Mathimix7/HueMix-Link/Hardware-designs/Gateway_v1.1/Gateway_v1.1_back.png

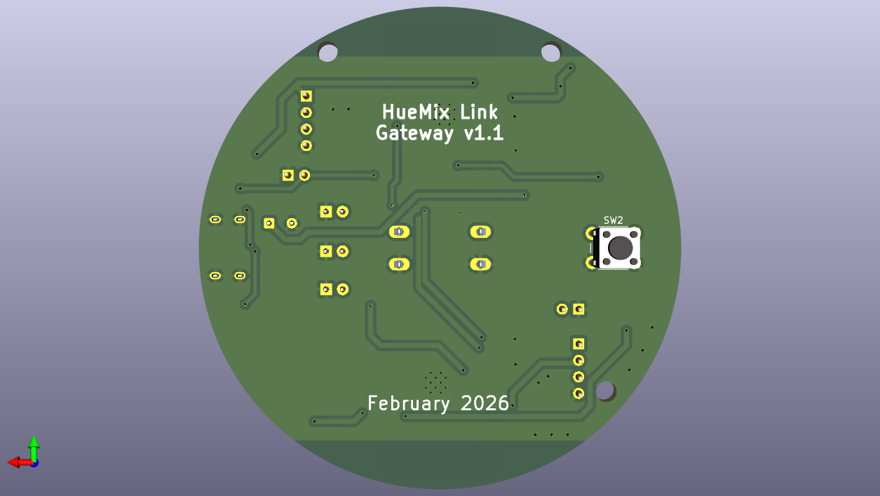
Hardware-designs/Gateway_v1.1/Gateway_v1.1_back.png
