Mathimix7/HueMix-Link/Hardware-designs/Magnetic Sensor/Magnetic Sensor-front.png

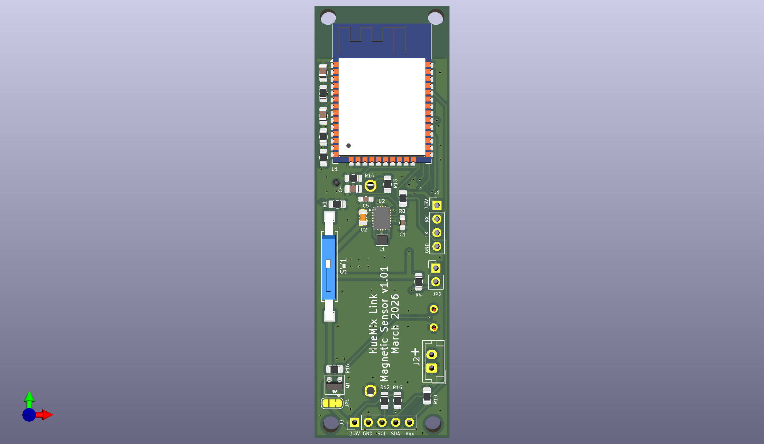
Hardware-designs/Magnetic Sensor/Magnetic Sensor-front.png
