Mathimix7/HueMix-Link/Hardware-designs/Motion_Sensor_v1.1/Motion_Sensor_v1.1_front.png

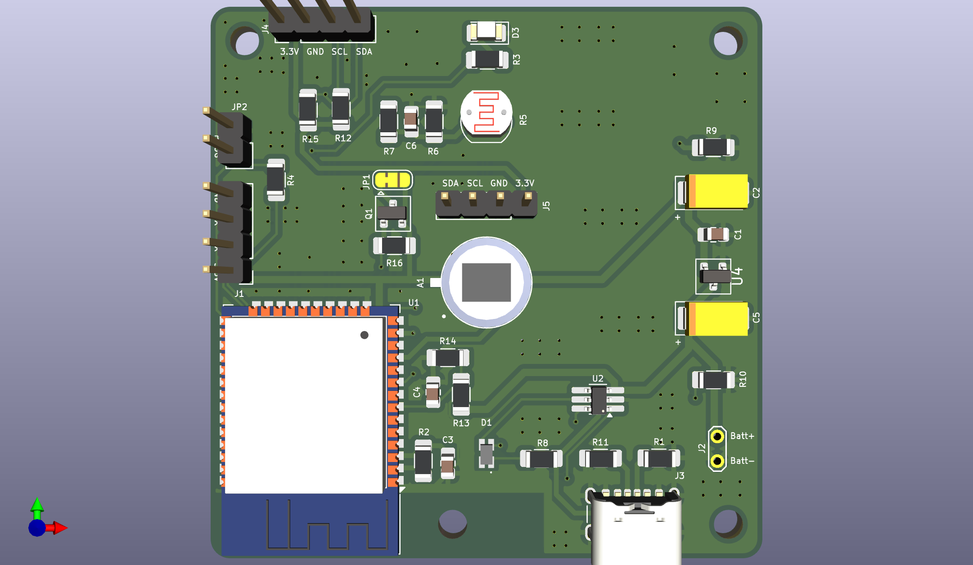
Hardware-designs/Motion_Sensor_v1.1/Motion_Sensor_v1.1_front.png
