Mathimix7/HueMix-Link/Hardware-designs/Normal_Button_v3/Normal_Button_v3_back.png

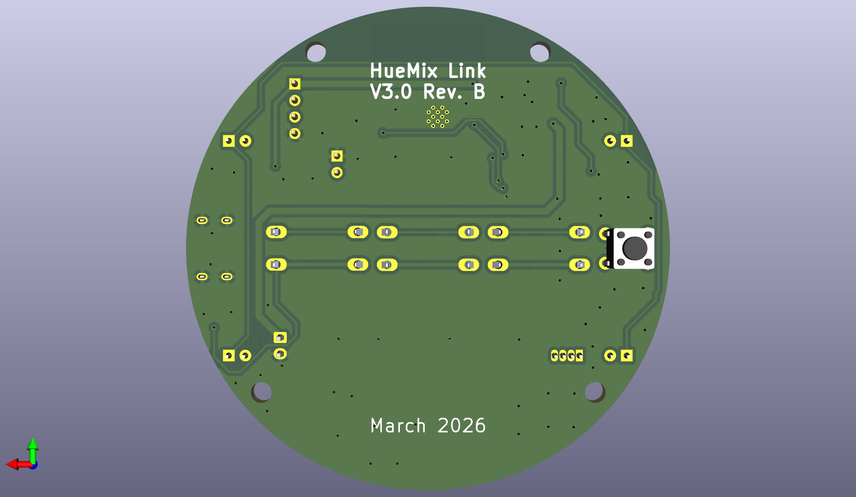
Hardware-designs/Normal_Button_v3/Normal_Button_v3_back.png
