Mathimix7/HueMix-Link/Hardware-designs/Magnetic Sensor/components/C1608X5R1A226M080AC/C1608X5R1A226M080AC.step

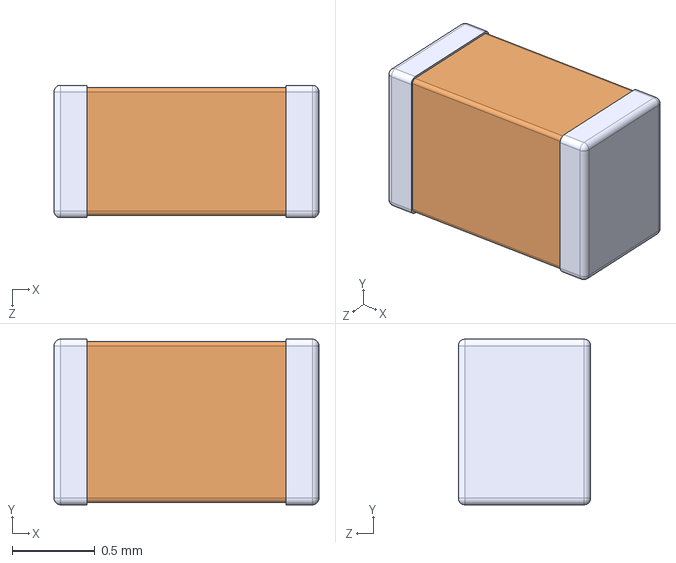
[picture p44: CAD file, 2026-03-12]
Hardware-designs/Magnetic Sensor/components/C1608X5R1A226M080AC/C1608X5R1A226M080AC.step
1.60 x 1.00 x 0.8 mm
