Mathimix7/HueMix-Link/Hardware-designs/Magnetic Sensor/components/IRA_S410ST01/IRA-S410ST01.step

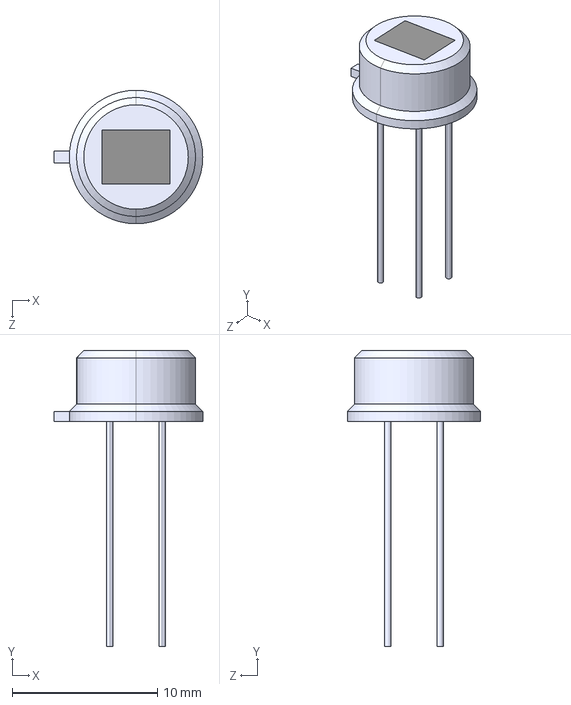
[picture p45: CAD file, 2026-02-21]
Hardware-designs/Magnetic Sensor/components/IRA_S410ST01/IRA-S410ST01.step
10.2 x 20.4 x 9.20 mm
