Mathimix7/HueMix-Link/Hardware-designs/Magnetic Sensor/components/MCP1700T_3302E_MB/SOT-23_MC_MCH.step

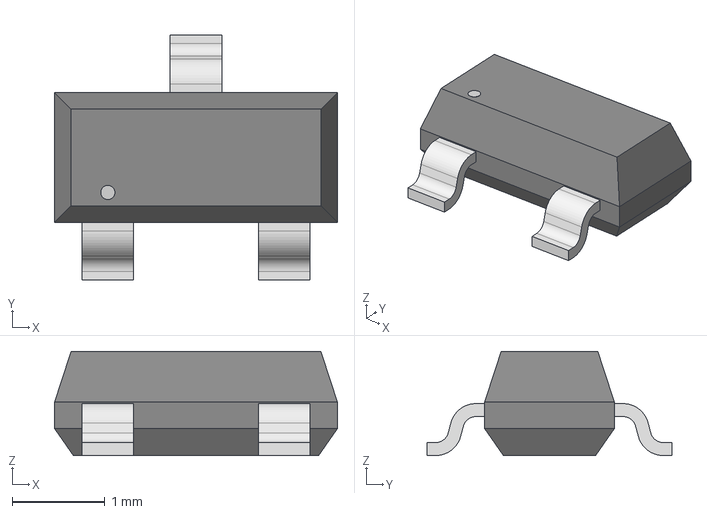
[picture p46: CAD file, 2026-02-21]
Hardware-designs/Magnetic Sensor/components/MCP1700T_3302E_MB/SOT-23_MC_MCH.step
3.05 x 2.64 x 1.12 mm
