Mathimix7/HueMix-Link/Hardware-designs/Magnetic Sensor/components/MSASJ21GBB5476MTNA01/MSASJ21GBB5476MTNA01.step

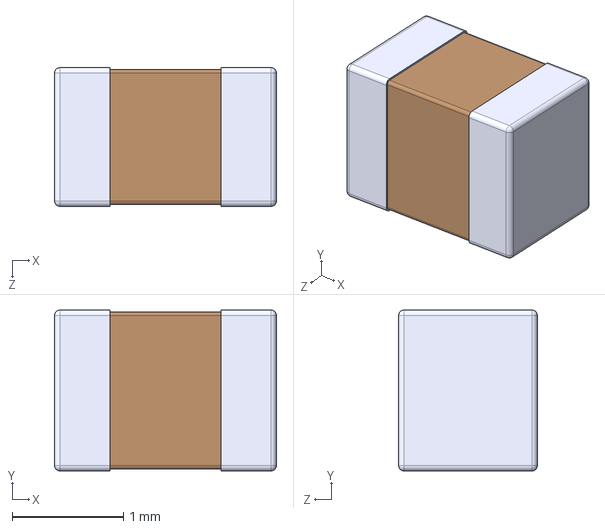
[picture p47: CAD file, 2026-03-12]
Hardware-designs/Magnetic Sensor/components/MSASJ21GBB5476MTNA01/MSASJ21GBB5476MTNA01.step
2.00 x 1.45 x 1.25 mm
