Mathimix7/HueMix-Link/Hardware-designs/Magnetic Sensor/components/Tantalum Cap/TAJC227K006RNJ.STEP

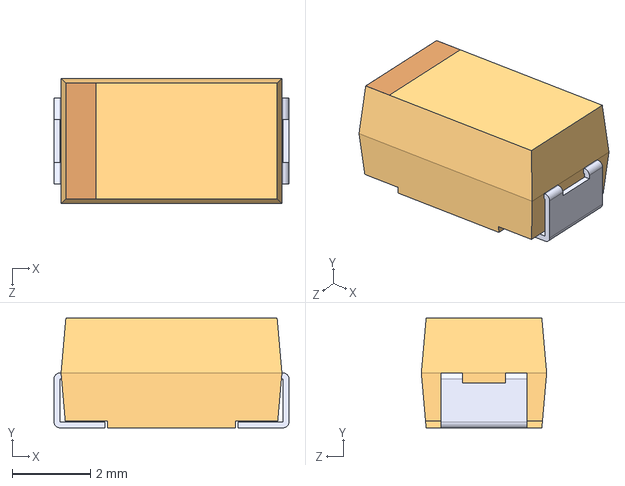
[picture p48: CAD file, 2026-02-21]
Hardware-designs/Magnetic Sensor/components/Tantalum Cap/TAJC227K006RNJ.STEP
6.00 x 2.80 x 3.20 mm
