Mathimix7/HueMix-Link/Hardware-designs/Magnetic Sensor/Magnetic Sensor.step

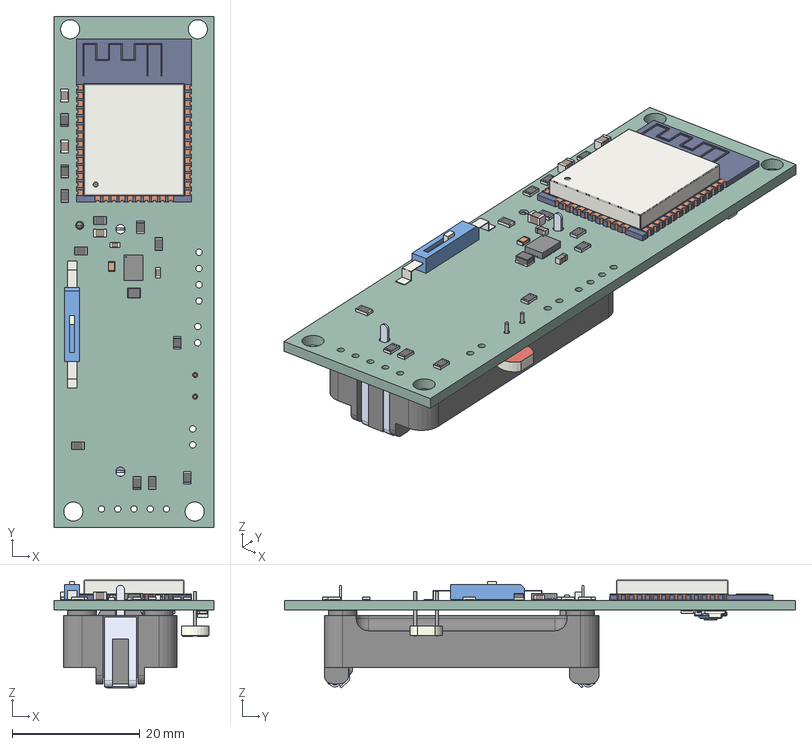
[picture p49: CAD file, 2026-03-29]
Hardware-designs/Magnetic Sensor/Magnetic Sensor.step
25.0 x 80.0 x 16.9 mm
L_Murata_DFE201610P
C1608X5R1A226M080AC
ESP32-WROOM-32
C_0805_2012Metric x 3
R_0805_2012Metric x 14
TPS63021DSJR
C_0603_1608Metric x 2
SW_SPST_REED_CT10_XXXX_G003
SW_SPST_REED_CT10_XXXX_G2
BH123A
R_LDR_5.1x4.3mm_P3.4mm_Vertical
PTS526SK15SMTR2_LFS
LED_1206_3216Metric
Magnetic Sensor_PCB
