Mathimix7/HueMix-Link/Hardware-designs/Motion_Sensor_v1.1/Motion_Sensor_v1.1.step

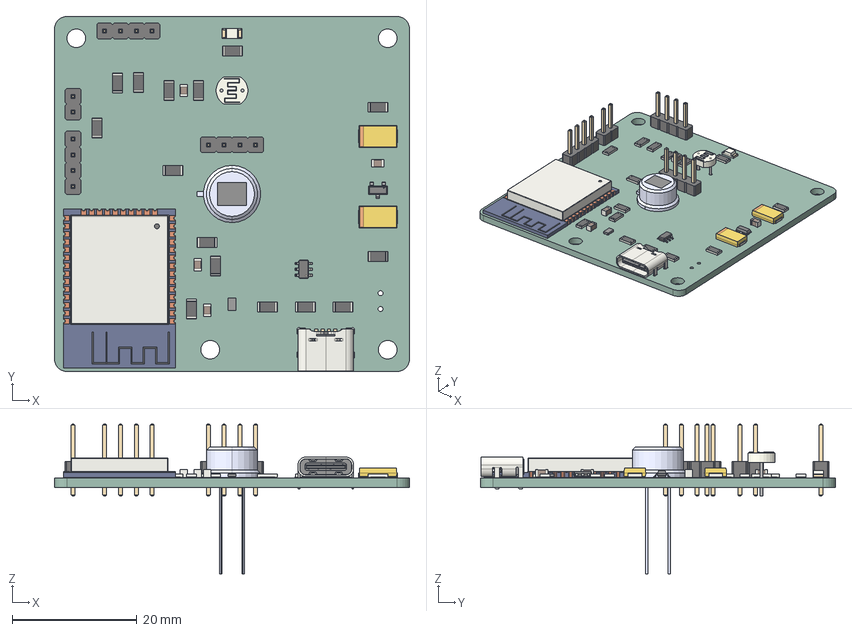
[picture p50: CAD file, 2026-02-21]
Hardware-designs/Motion_Sensor_v1.1/Motion_Sensor_v1.1.step
57.0 x 57.0 x 24.0 mm
R_1206_3216Metric x 15
C_0805_2012Metric x 4
USB_C_Receptacle_GCT_USB4125-xx-x-0190_6P_TopMnt_Horizontal
TSOT-23-6
LED_1206_3216Metric
PinHeader_1x02_P2.54mm_Vertical
IRA-S410ST01
CP_EIA-6032-15_Kemet-U x 2
SOT-23_MC_MCH
ESP32-WROOM-32
PinHeader_1x04_P2.54mm_Vertical x 3
R_LDR_5.1x4.3mm_P3.4mm_Vertical
Pins
Motion_Sensor_v1.1_PCB
