Mathimix7/HueMix-Link/Hardware-designs/Normal_Button_v3/components/ESP32 3D/ESP32-WROOM-32E-N8.STEP

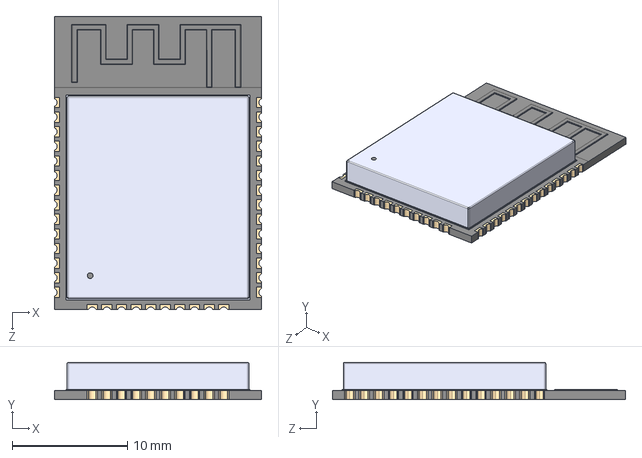
[picture p51: CAD file, 2026-02-21]
Hardware-designs/Normal_Button_v3/components/ESP32 3D/ESP32-WROOM-32E-N8.STEP
18.0 x 3.25 x 25.5 mm
