Mathimix7/HueMix-Link/Hardware-designs/Normal_Button_v3/Normal_Button_v3.step

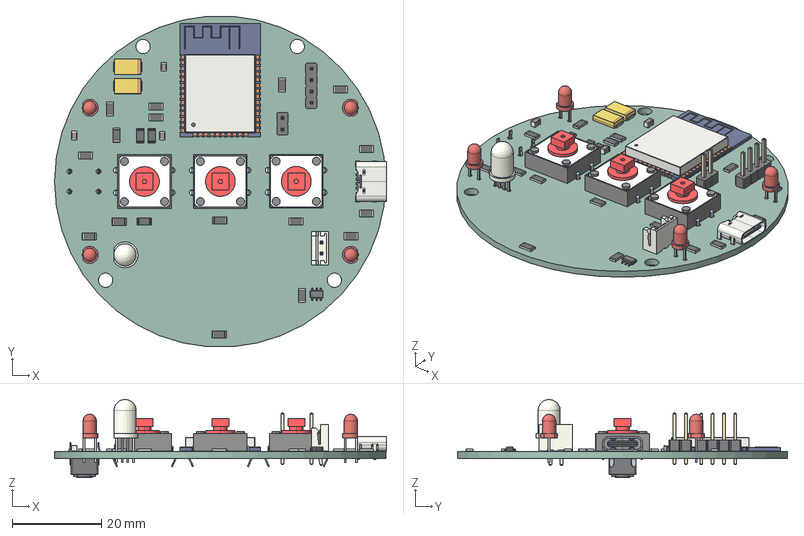
[picture p52: CAD file, 2026-03-01]
Hardware-designs/Normal_Button_v3/Normal_Button_v3.step
74.3 x 74.0 x 17.5 mm
R_1206_3216Metric x 19
TSOT-23-6
USB_C_Receptacle_GCT_USB4125-xx-x-0190_6P_TopMnt_Horizontal
LED_D3.0mm x 4
PinHeader_1x04_P2.54mm_Vertical
SW_PUSH_6mm
Body002 (Mirror #1) x 3
Body003 (Mirror #2) x 3
CP_EIA-6032-15_Kemet-U x 2
C_0805_2012Metric x 3
ESP32-WROOM-32
PinHeader_1x02_P2.54mm_Vertical
LED_D5.0mm-4_RGB
JST_EH_B2B-EH-A_1x02_P2.50mm_Vertical
Normal_Button_v3_PCB
