Mathimix7/HueMix-Link/Hardware-designs/Remote_4button_v1/Remote_4button_v1.step

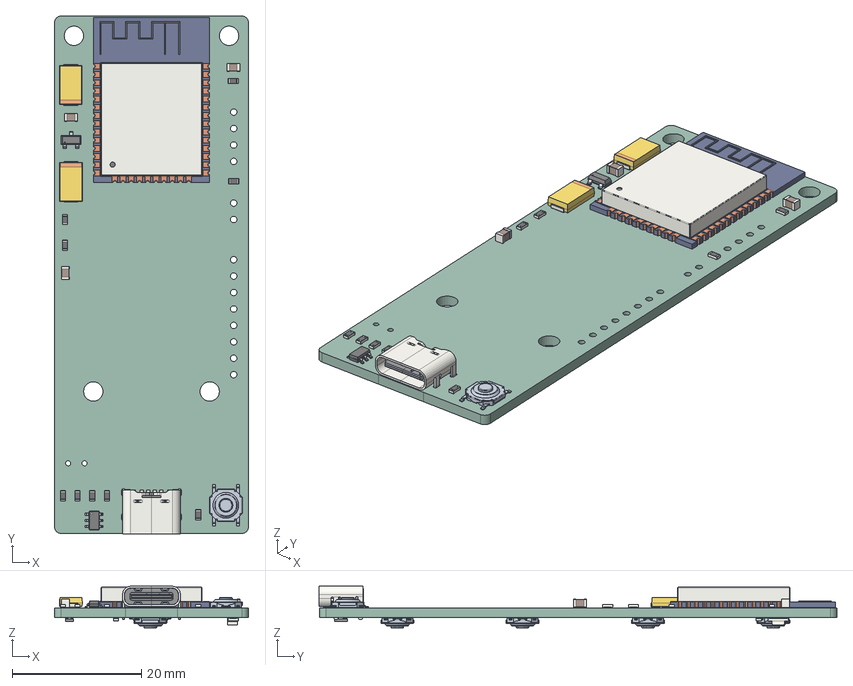
[picture p53: CAD file, 2026-02-21]
Hardware-designs/Remote_4button_v1/Remote_4button_v1.step
30.0 x 80.1 x 6.44 mm
R_0603_1608Metric x 14
C_0805_2012Metric x 3
USB_C_Receptacle_GCT_USB4125-xx-x-0190_6P_TopMnt_Horizontal
PTS526SK15SMTR2_LFS x 5
TSOT-23-6
CP_EIA-6032-15_Kemet-U x 2
SOT-23_MC_MCH
ESP32-WROOM-32
LED_1206_3216Metric
Pins
Remote_4button_v1_PCB
