Mathimix7/HueMix-Link/3D Files/Buttons/1_Button/Lid_1_Button.stl

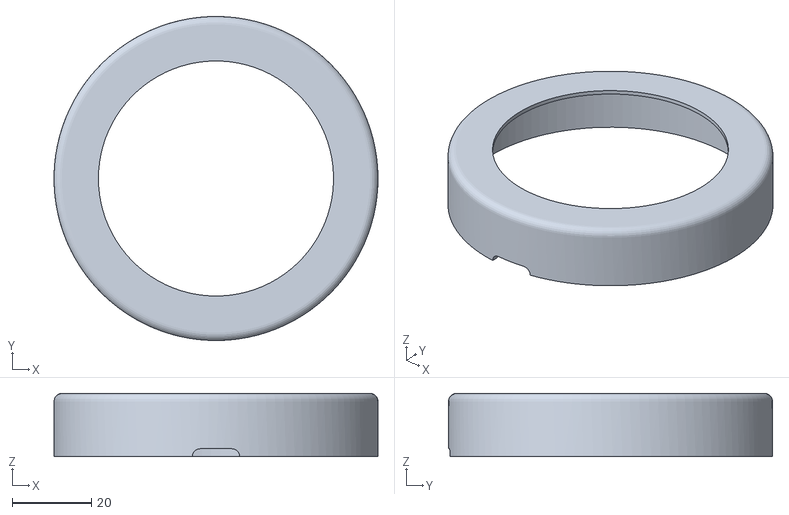
[picture p54: CAD file, 2026-04-03]
3D Files/Buttons/1_Button/Lid_1_Button.stl
82.0 x 82.0 x 16.0
