Mathimix7/HueMix-Link/3D Files/Door Sensor/Box Magnetic Sensor.stl

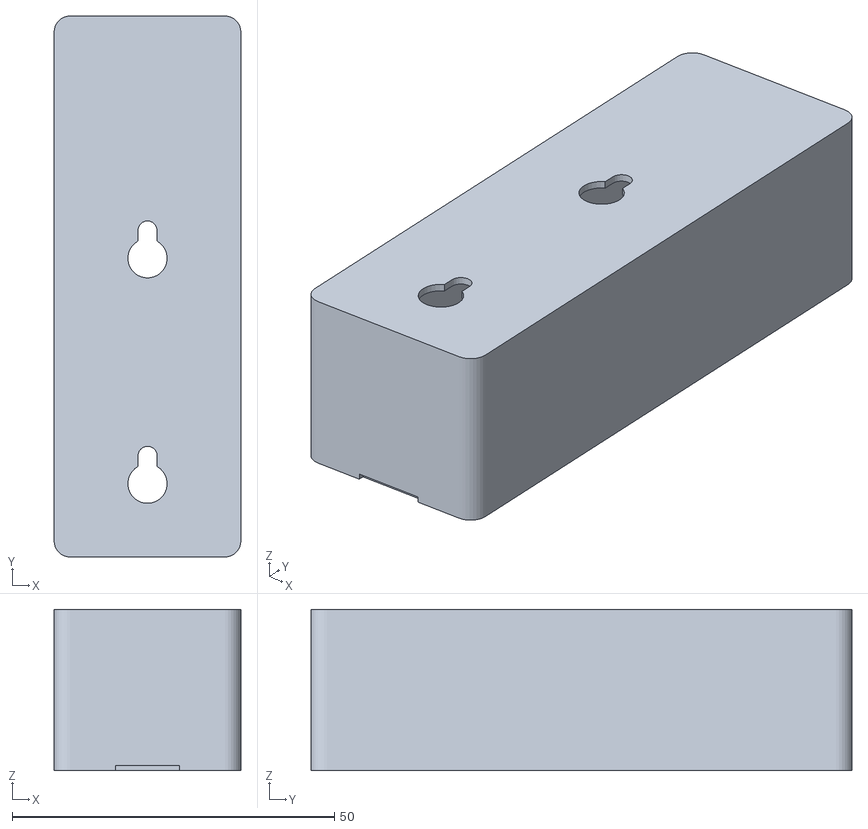
[picture p55: CAD file, 2026-04-03]
3D Files/Door Sensor/Box Magnetic Sensor.stl
29.0 x 84.0 x 25.0
