Mathimix7/HueMix-Link/3D Files/Lightstrip/Lid Lightstrip controller.stl

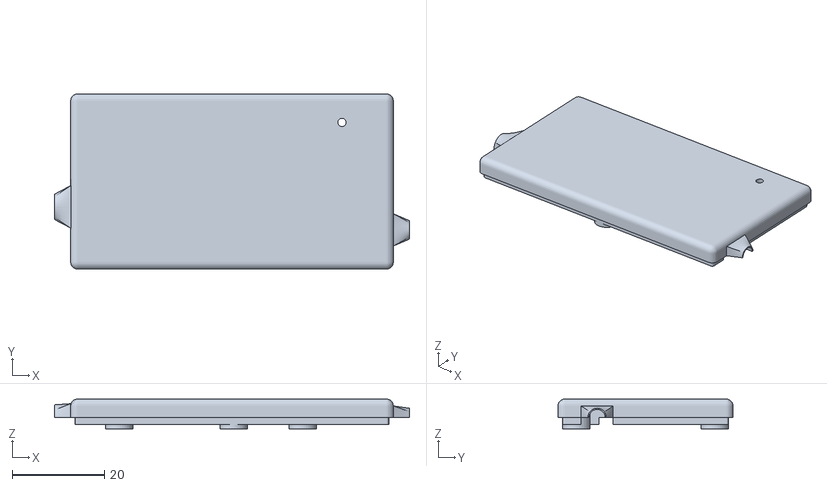
[picture p56: CAD file, 2026-04-03]
3D Files/Lightstrip/Lid Lightstrip controller.stl
77.0 x 38.0 x 6.50
