Mathimix7/HueMix-Link/3D Files/Motion Sensor/Holder Motion Sensor_slim.stl

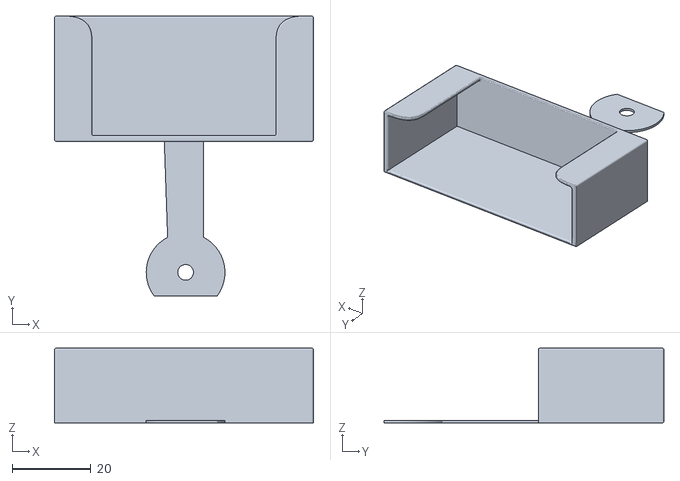
[picture p57: CAD file, 2026-04-03]
3D Files/Motion Sensor/Holder Motion Sensor_slim.stl
65.8 x 71.1 x 19.0
