Mathimix7/HueMix-Link/3D Files/Remote/Remote Base.stl

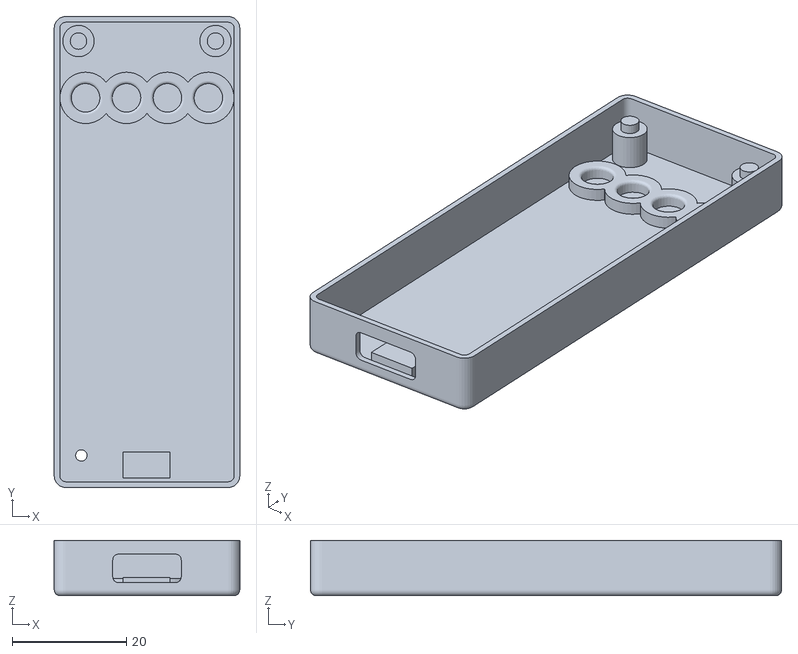
[picture p58: CAD file, 2026-04-03]
3D Files/Remote/Remote Base.stl
32.5 x 82.5 x 9.70
