Mathimix7/HueMix-Link/3D Files/Buttons/1_Button/Axle_1_Button.stl

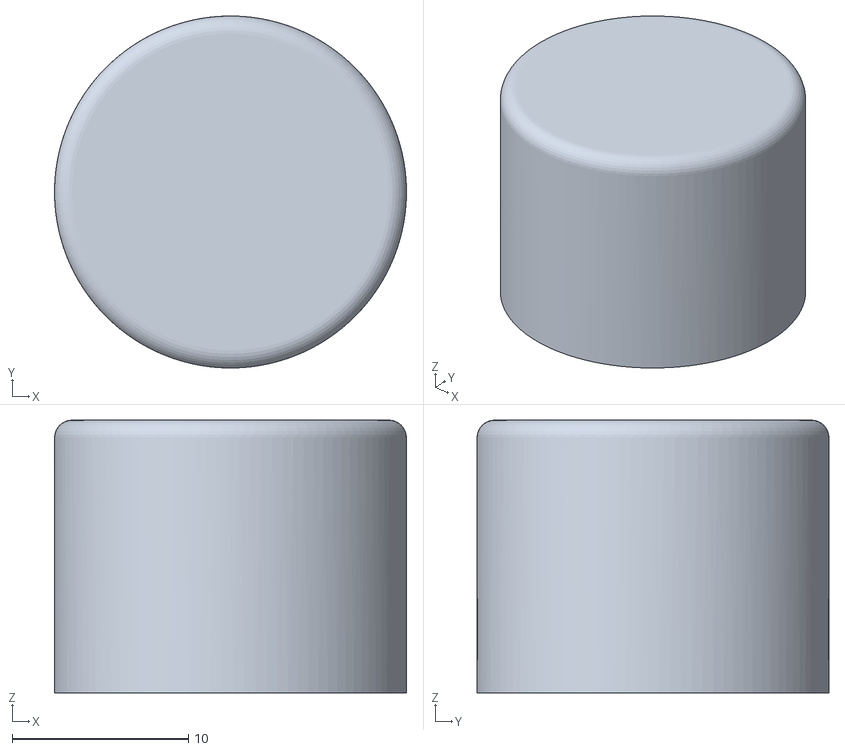
[picture p59: CAD file, 2026-04-03]
3D Files/Buttons/1_Button/Axle_1_Button.stl
20.0 x 20.0 x 15.5
