Mathimix7/HueMix-Link/3D Files/Buttons/2_Button/Square button_2 buttons.stl

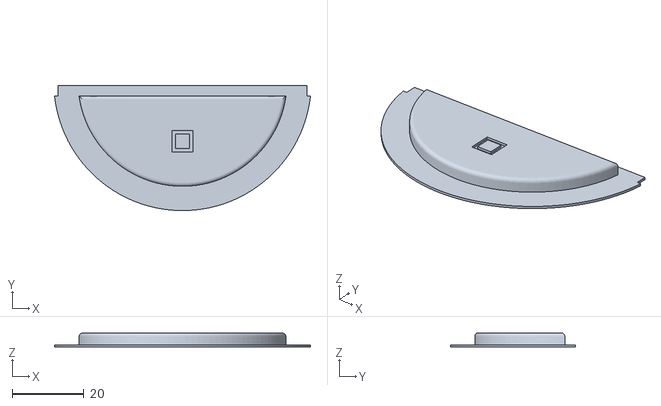
[picture p60: CAD file, 2026-04-03]
3D Files/Buttons/2_Button/Square button_2 buttons.stl
71.6 x 35.0 x 4.00
