Mathimix7/HueMix-Link/3D Files/Door Sensor/Holder Magnetic Sensor.stl

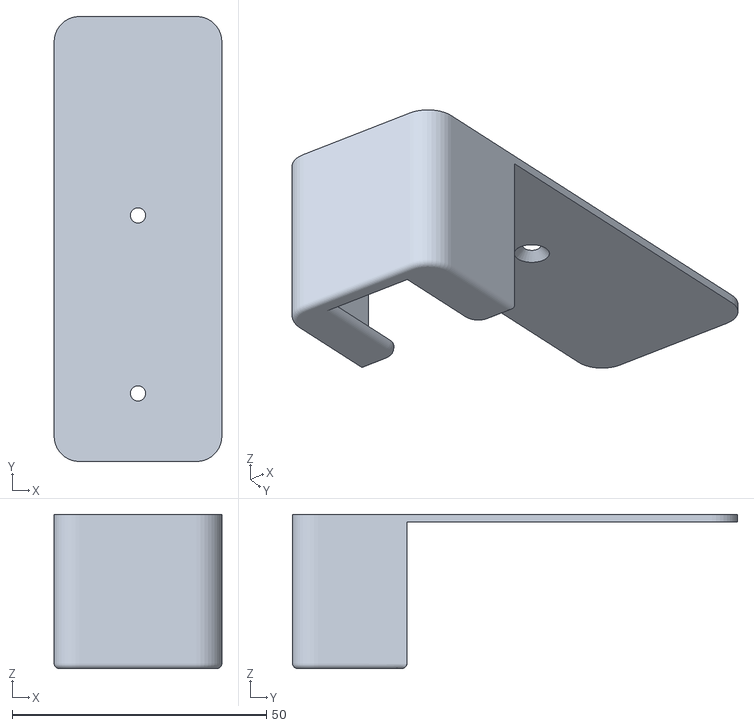
[picture p61: CAD file, 2026-04-03]
3D Files/Door Sensor/Holder Magnetic Sensor.stl
33.0 x 87.5 x 30.3
