Mathimix7/HueMix-Link/3D Files/Motion Sensor/Base Motion Sensor.stl

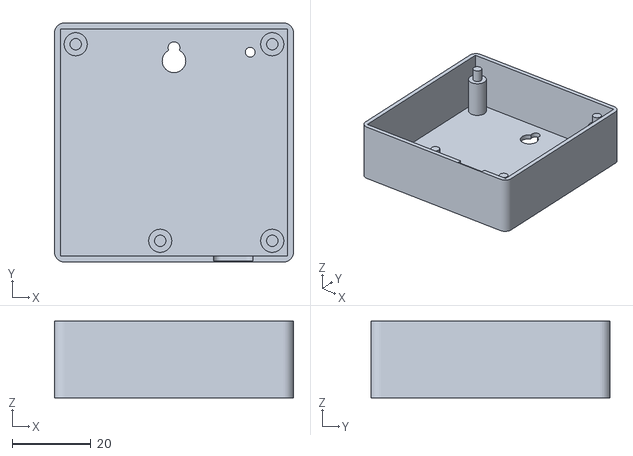
[picture p62: CAD file, 2026-04-03]
3D Files/Motion Sensor/Base Motion Sensor.stl
60.8 x 60.8 x 19.5
