Mathimix7/HueMix-Link/3D Files/Remote/Remote Lid.stl

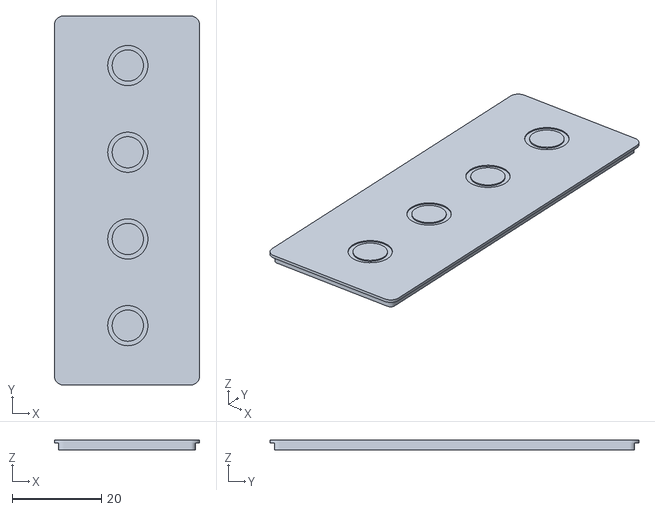
[picture p63: CAD file, 2026-04-03]
3D Files/Remote/Remote Lid.stl
32.5 x 82.5 x 2.20
