Mathimix7/HueMix-Link/3D Files/Buttons/3_Button/Lid_3 buttons.stl

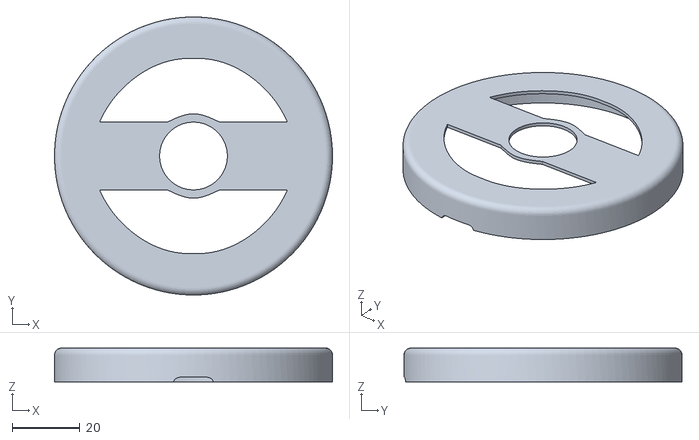
[picture p65: CAD file, 2026-04-03]
3D Files/Buttons/3_Button/Lid_3 buttons.stl
82.0 x 82.0 x 10.0
