Mathimix7/HueMix-Link/3D Files/Motion Sensor/Base Motion Sensor_slim.stl

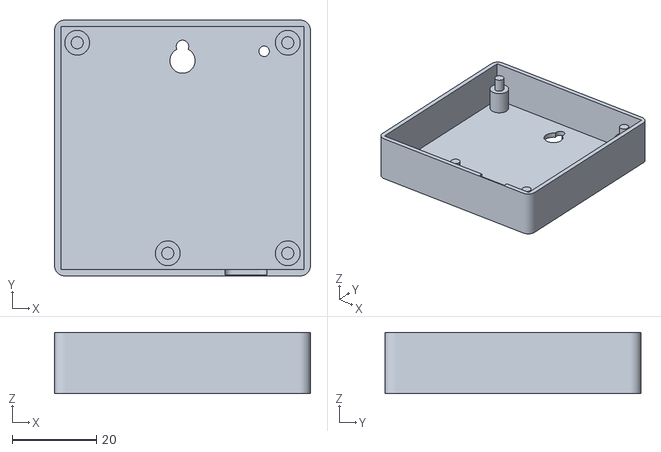
[picture p66: CAD file, 2026-04-03]
3D Files/Motion Sensor/Base Motion Sensor_slim.stl
60.8 x 60.8 x 14.5
