Mathimix7/HueMix-Link/3D Files/Buttons/3_Button/Square button_3 buttons.stl

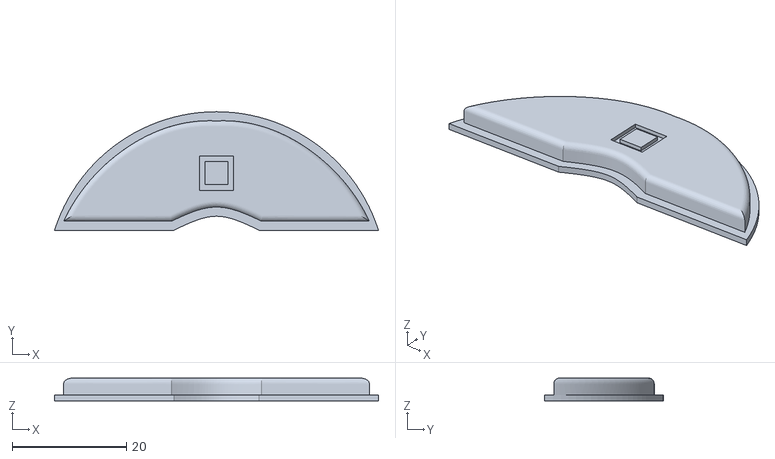
[picture p67: CAD file, 2026-04-03]
3D Files/Buttons/3_Button/Square button_3 buttons.stl
56.7 x 20.8 x 4.00
