Mathimix7/HueMix-Link/3D Files/Buttons/2_Button/Lid_2 buttons.stl

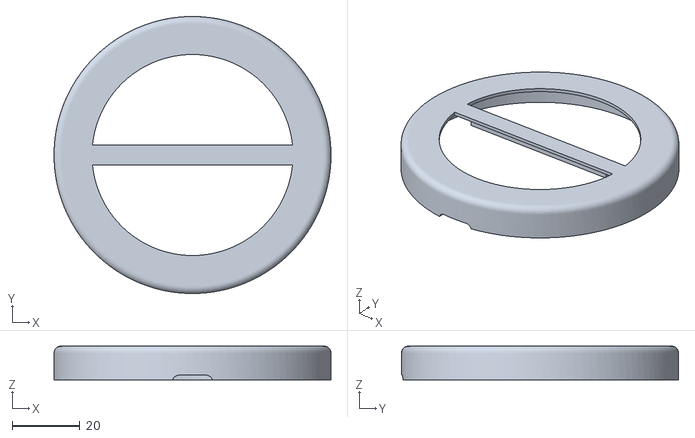
[picture p68: CAD file, 2026-04-03]
3D Files/Buttons/2_Button/Lid_2 buttons.stl
82.0 x 82.0 x 10.0
