Mathimix7/HueMix-Link/3D Files/Buttons/3_Button/Center button_3 buttons.stl

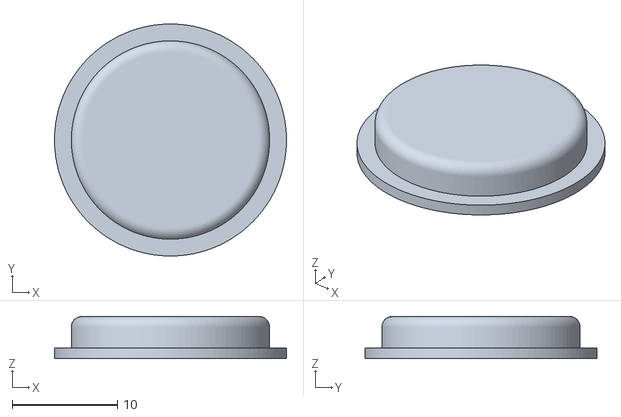
[picture p69: CAD file, 2026-04-03]
3D Files/Buttons/3_Button/Center button_3 buttons.stl
22.0 x 22.0 x 4.00
